jogarman/TFG/Organigramas/diagrama P1.png

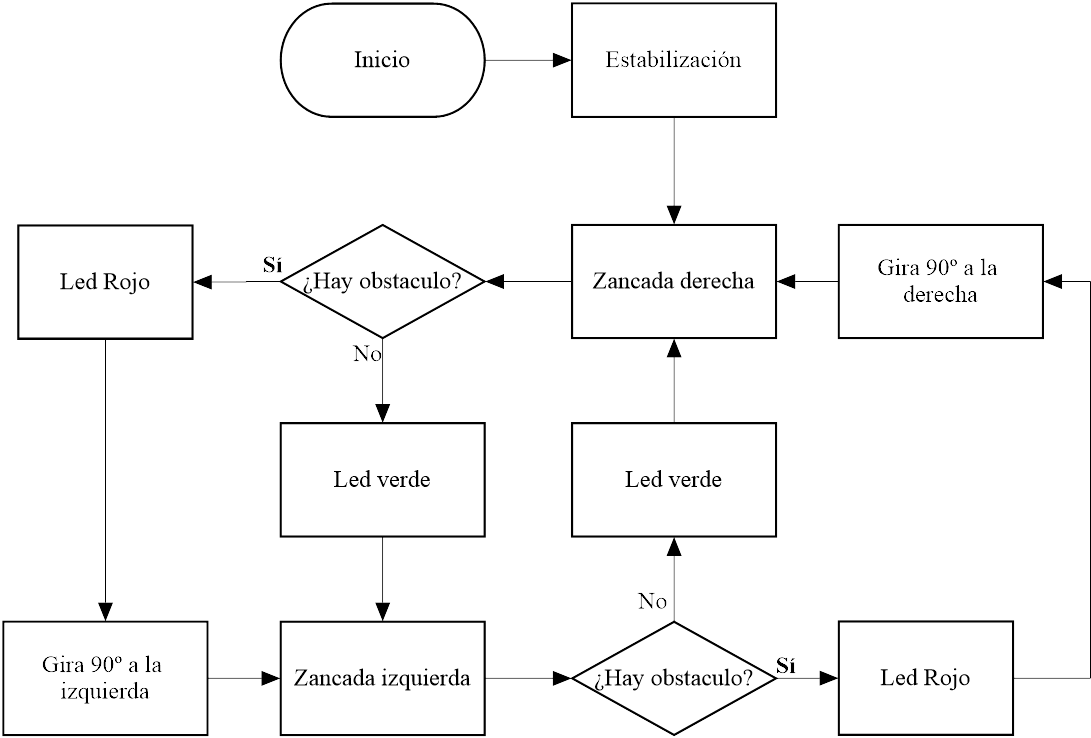
Organigramas/diagrama P1.png
