jogarman/TFG/Organigramas/tomarDatosMPU.png

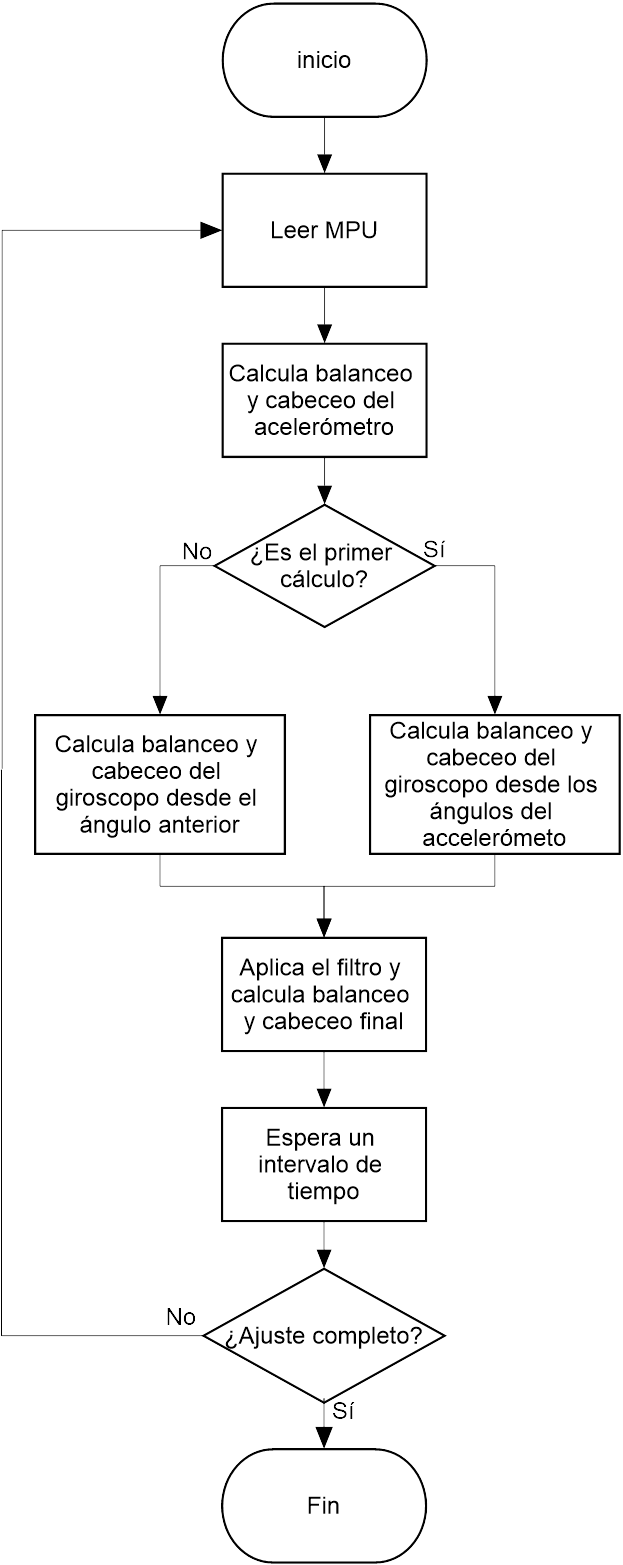
Organigramas/tomarDatosMPU.png
