jogarman/TFG/Planos eléctricos/Plano electrico alimentacion servos.png

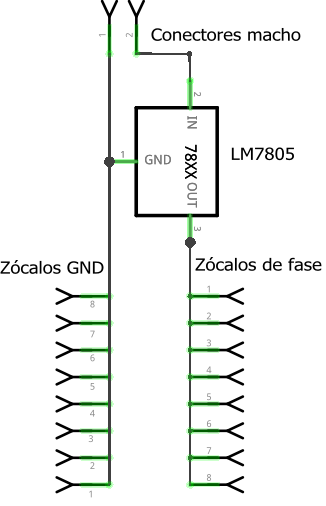
Planos eléctricos/Plano electrico alimentacion servos.png
