jogarman/TFG/Planos eléctricos/Grafico de montaje.png

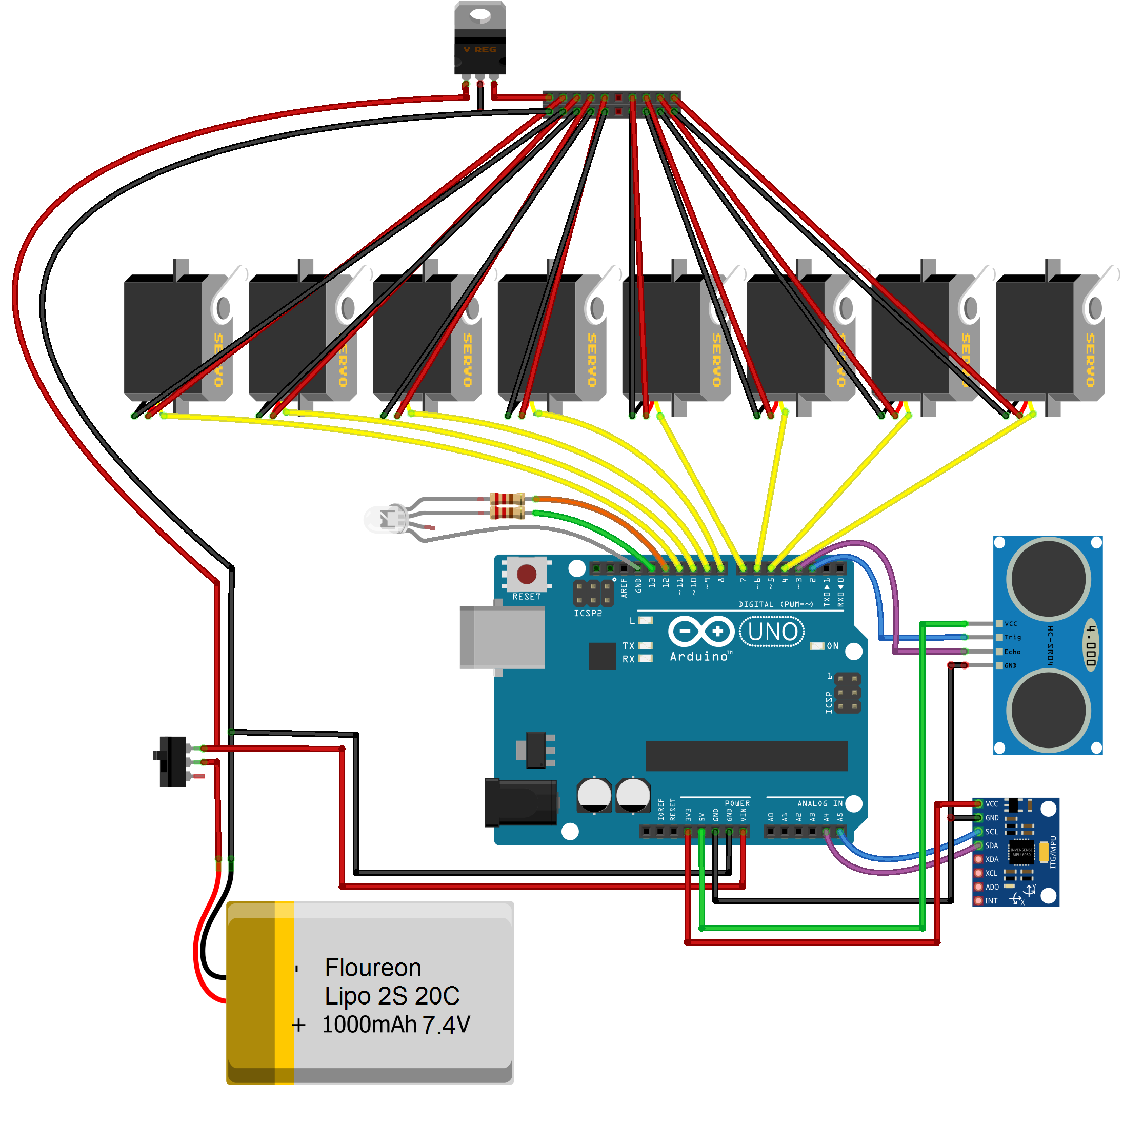
Planos eléctricos/Grafico de montaje.png
